albertito1998/wheather-station/Impresion 3D/pluviometro/balancin.stl

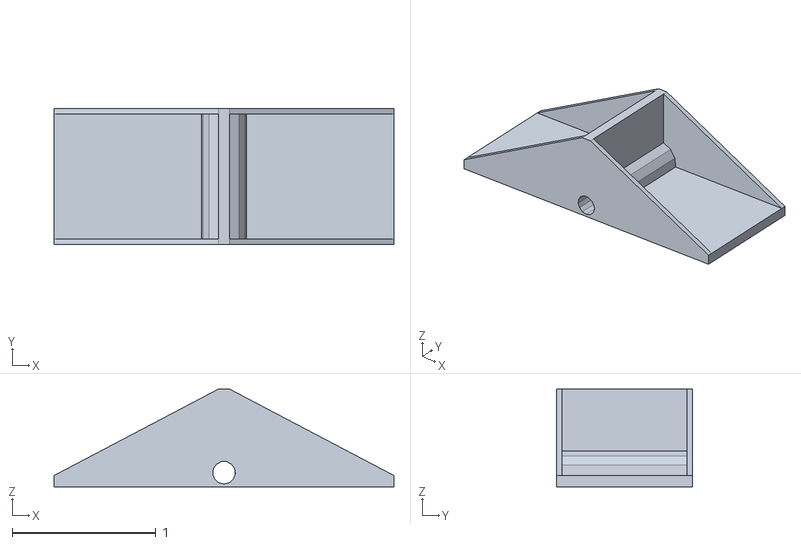
[picture p18: CAD file, 2022-06-29]
Impresion 3D/pluviometro/balancin.stl
2.36 x 0.945 x 0.679
