albertito1998/wheather-station/Impresion 3D/veleta/cover_veleta.stl

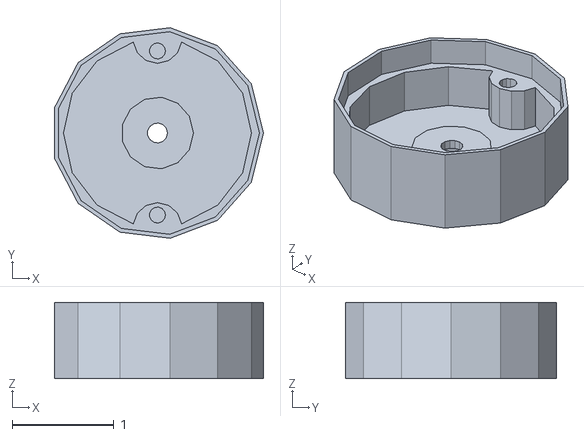
[picture p19: CAD file, 2022-06-29]
Impresion 3D/veleta/cover_veleta.stl
2.06 x 2.07 x 0.748
