albertito1998/wheather-station/Impresion 3D/anemometro/rotor.stl

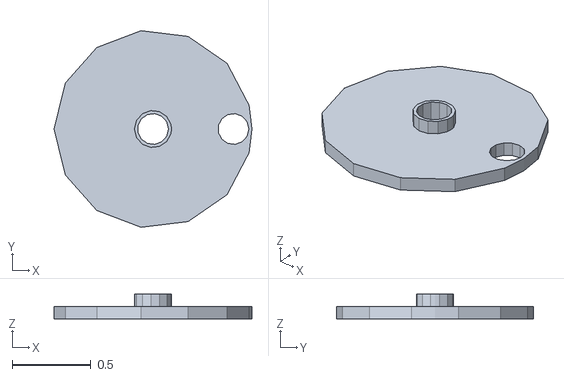
[picture p20: CAD file, 2022-06-29]
Impresion 3D/anemometro/rotor.stl
1.26 x 1.25 x 0.157
