albertito1998/wheather-station/Impresion 3D/veleta/eje_veleta.stl

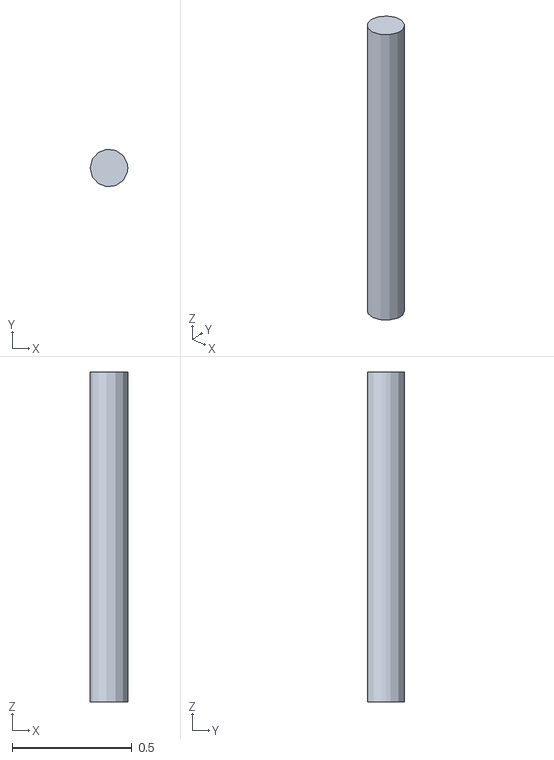
[picture p21: CAD file, 2022-06-29]
Impresion 3D/veleta/eje_veleta.stl
0.157 x 0.156 x 1.38
