albertito1998/wheather-station/Impresion 3D/anemometro/cap.stl

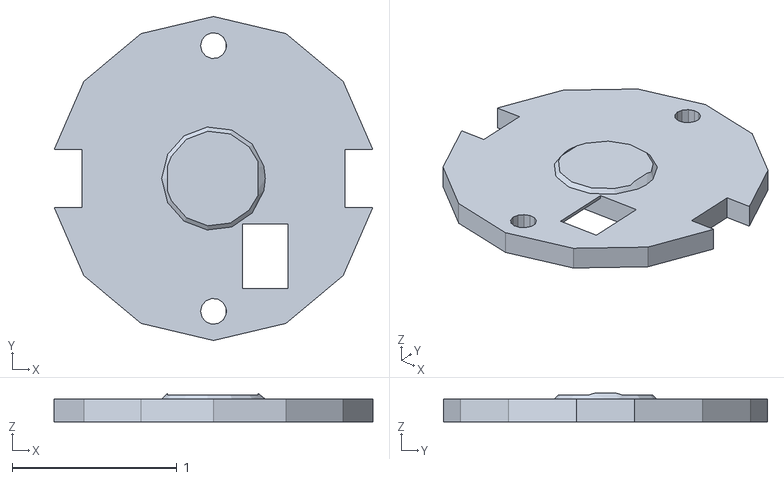
[picture p22: CAD file, 2022-06-29]
Impresion 3D/anemometro/cap.stl
1.94 x 1.97 x 0.174
