albertito1998/wheather-station/Impresion 3D/veleta/body_veleta.stl

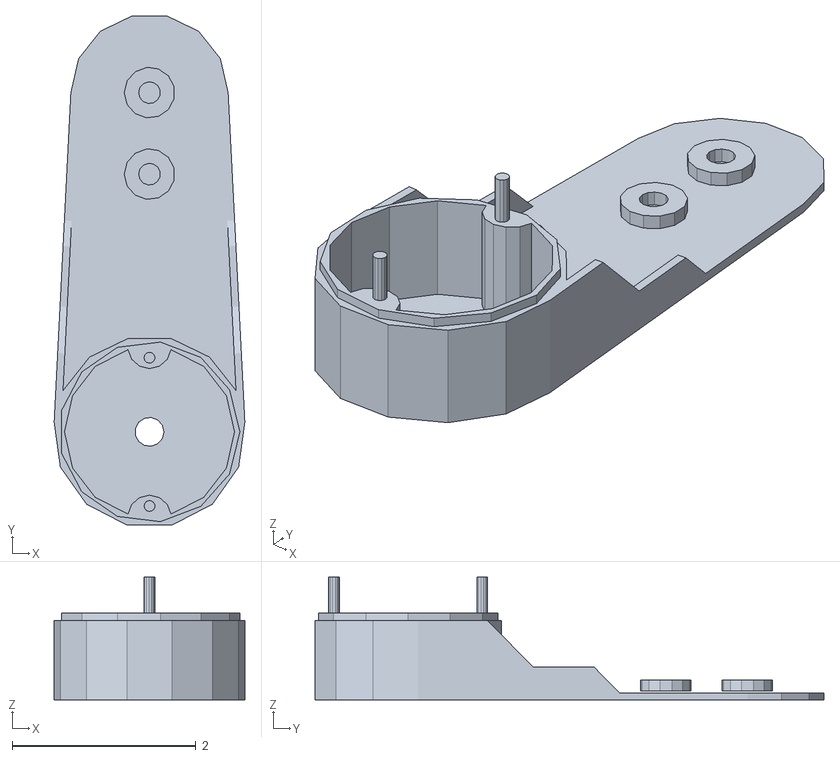
[picture p23: CAD file, 2022-06-29]
Impresion 3D/veleta/body_veleta.stl
2.08 x 5.54 x 1.34
