albertito1998/wheather-station/Impresion 3D/anemometro/union_pala_rotor.stl

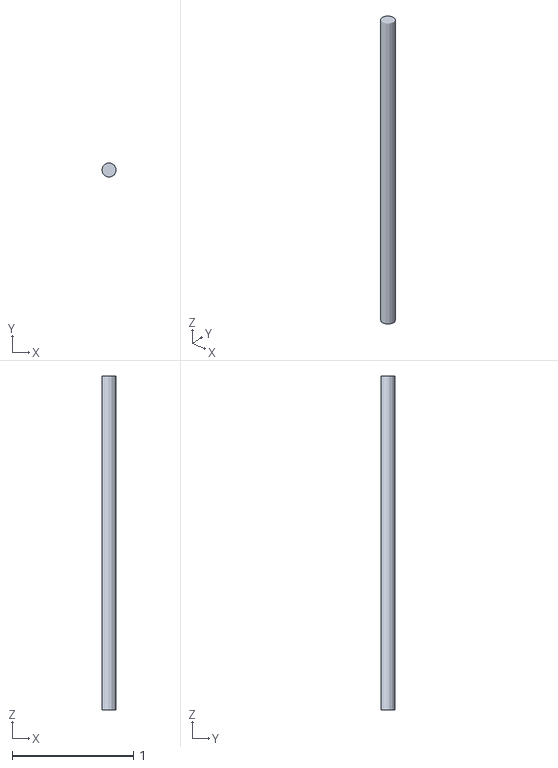
[picture p24: CAD file, 2022-06-29]
Impresion 3D/anemometro/union_pala_rotor.stl
0.118 x 0.117 x 2.76
